waterloo-rocketry/curing-oven/03 - Software/Data/Modular Curing Oven_CD.pdf

# Our Project

A temperature-controlled curing oven for composite materials that is modular, safe, and easy to store

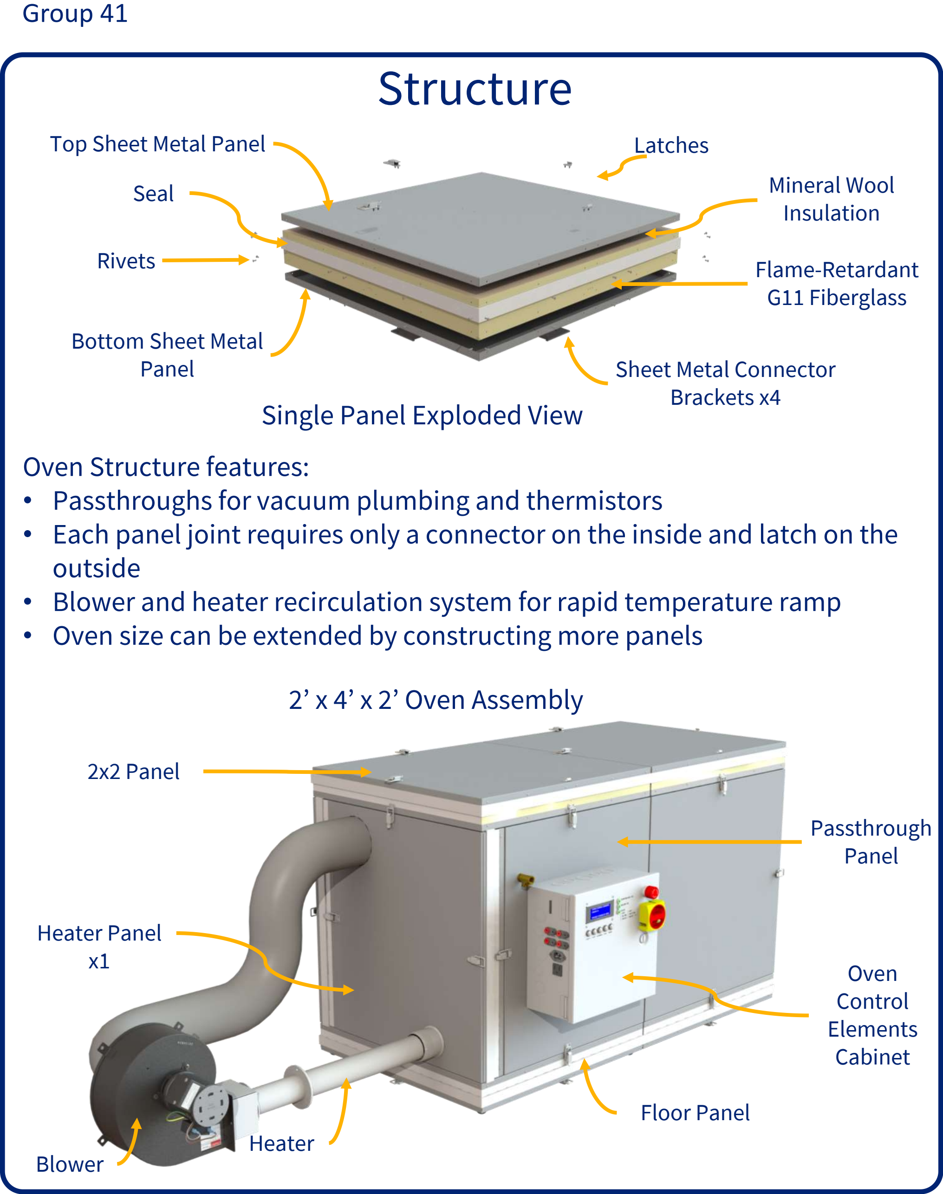
[picture p3: figure]
Group 41; Top Sheet Metal Panel; Latches; Bottom Sheet Metal Panel; Seal; Flame-Retardant G11 Fiberglass; Mineral Wool Insulation; Sheet Metal Connector Brackets x4; Rivets; Single Panel Exploded View; Oven Structure features:; outside; 2’ x 4’ x 2’ Oven Assembly; Blower; Heater; Heater Panel x1; Floor Panel; Oven Control Elements Cabinet; Passthrough Panel; 2x2 Panel
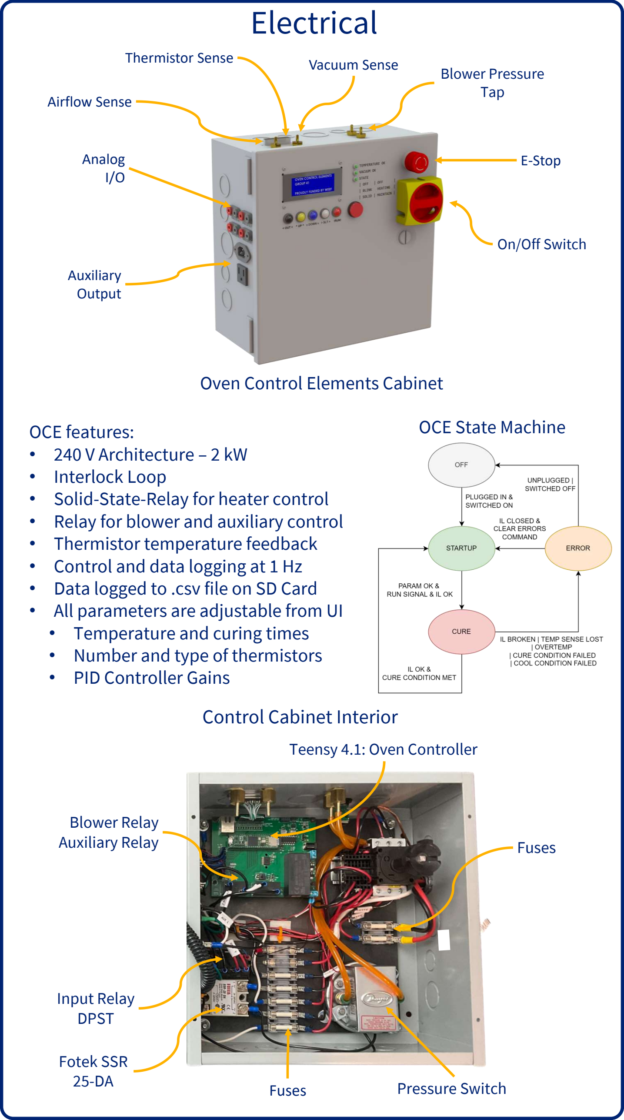
[picture p4: figure]
Control Cabinet Interior; OCE features: • 240 V Architecture – 2 kW • Interlock Loop • Solid-State-Relay for heater control; • Thermistor temperature feedback • Control and data logging at 1 Hz • Data logged to .csv file on SD Card • All parameters are adjustable from UI • Temperature and curing times • Number and type of thermistors • PID Controller Gains; Teensy 4.1: Oven Controller; Blower Relay Auxiliary Relay; Fuses; Pressure Switch; Fotek SSR 25-DA; Input Relay DPST; OCE State Machine; Oven Control Elements Cabinet; Vacuum Sense; Thermistor Sense; Airflow Sense; Blower Pressure Tap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

Structure | Electrical

# Modular Composites Curing Oven

# Testing

# Motivation

- Student design teams in the Sedra Student Design Center at UW work on composites parts that span a wide range of geometries and sizes, and lack the ability to cure parts at temperature
- Most high-performance composite materials must be cured in controlled temperature environments
- Curing ovens are generally expensive, take up large amounts of space, and can be difficult to control

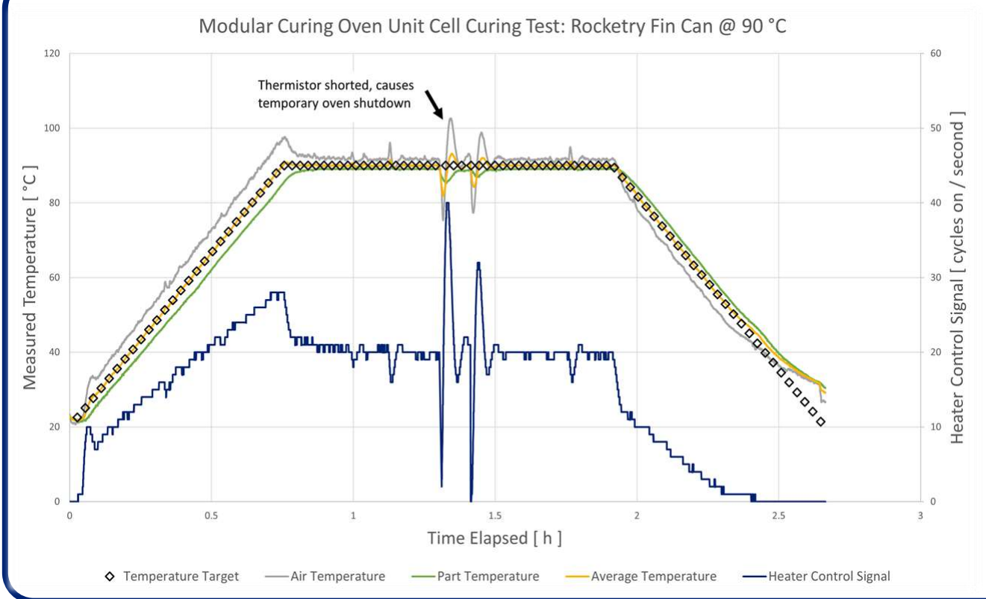
[picture p5: figure]

# Sponsors

Room-sized
industrial oven

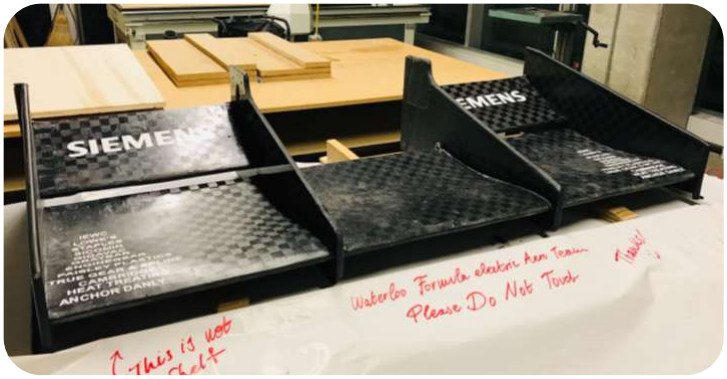
[picture p6: figure]

Low temp
recycling bin oven

High pressure autoclave
for Boeing 77X

# Existing Solutions:

Rocketry Fin Can

Formula Electric Front Wing

Design Objectives | Specifications | Value | Unit | Results
Functionality | Temperature Uniformity | ± 5 | °C | Pass
Functionality | Service Life | ≥ 10 | year | N/A
Functionality | Temperature Ramp Rate | ≥ 2 | °C/min | N/A
Safety | Structure and Ducting Surface Temperature | ≤ 30 | °C | Fail
Safety | Maximum Air Temperature ≤ 200 | °C | Pass
User Friendliness Assembly Time | ≤ 15 | min | Pass

Power Source: 240 V
Resin: Airstone 780E
Cure Schedule: 1 hr
@ 90 °C 45 min.
ramp
Temperature Error:
< 5 °C at steady state

The rocketry fin can was post-cured in the curing oven to obtain better structural properties at the high temperatures observed in the desert at competition in New Mexico.

- Passthroughs for vacuum plumbing and thermistors
- Each panel joint requires only a connector on the inside and latch on the
- Blower and heater recirculation system for rapid temperature ramp
- Oven size can be extended by constructing more panels
- Relay for blower and auxiliary control

Hamza Abu Abah
Calvin DeKoter
Shirley Kong
Nicolas Vrban
Yang Tina Zhang
