waterloo-rocketry/curing-oven/03 - Software/Data/AX-5201XL_curecycle.png

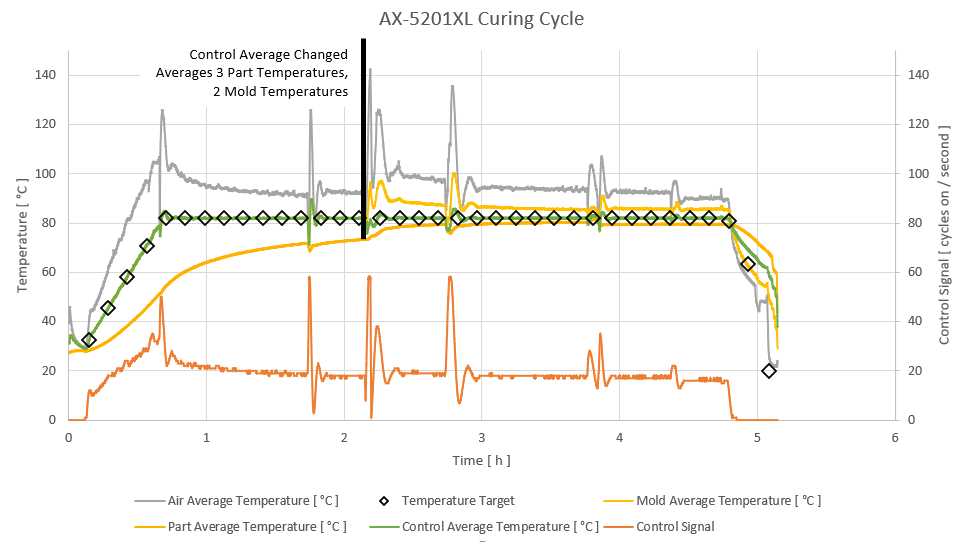
03 - Software/Data/AX-5201XL_curecycle.png
