waterloo-rocketry/curing-oven/03 - Software/Data/fincangraph.png

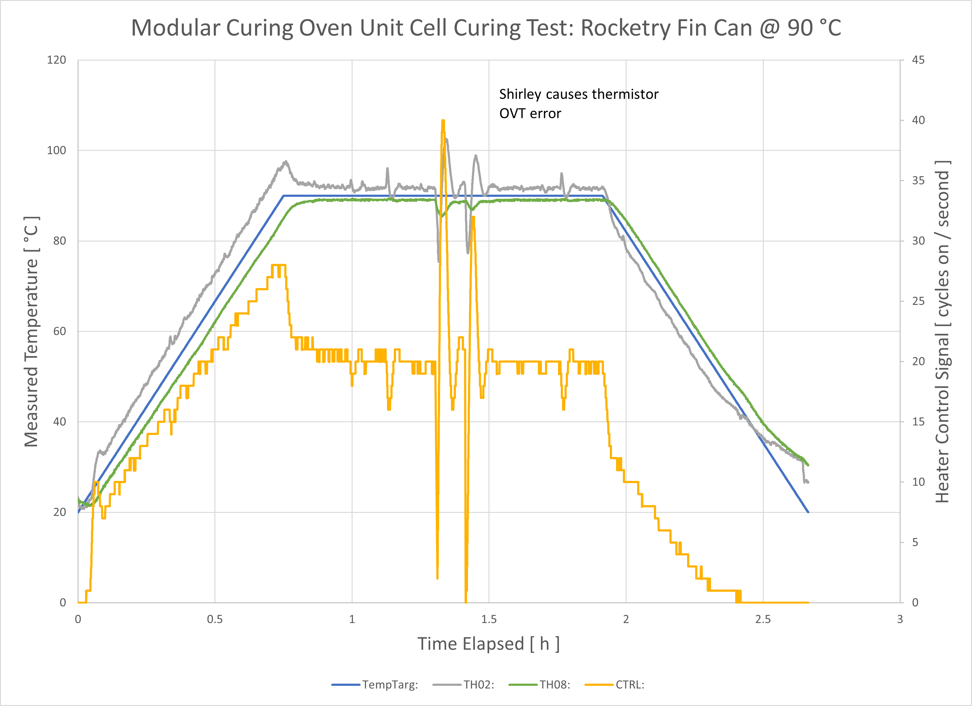
03 - Software/Data/fincangraph.png
