waterloo-rocketry/curing-oven/03 - Software/Data/fincangraph_temperror.png

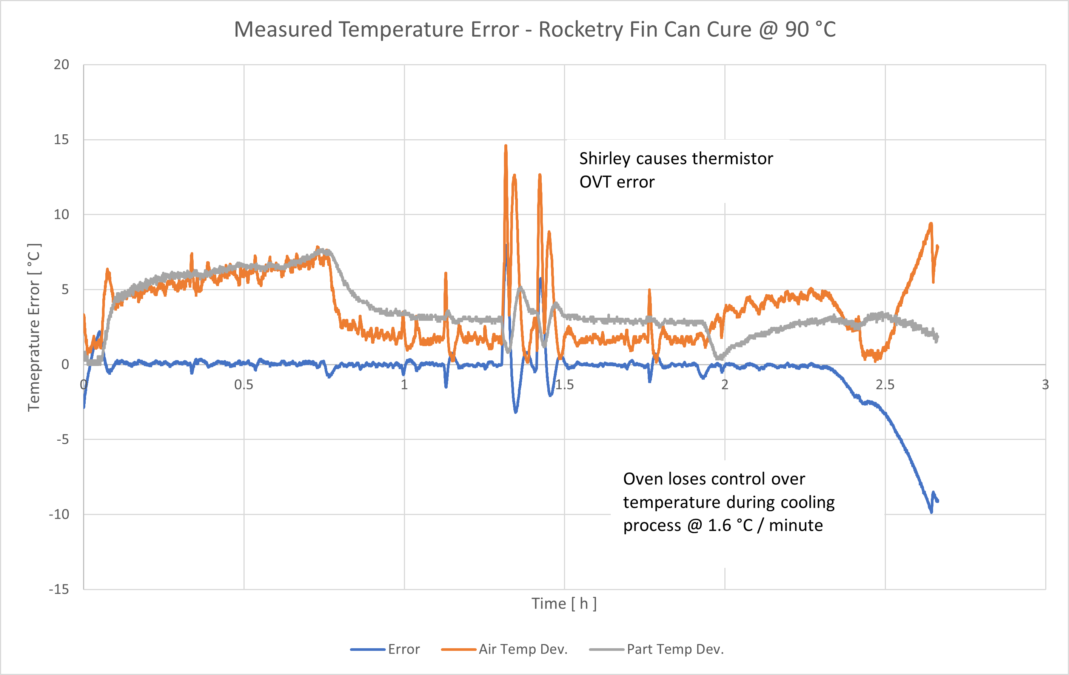
03 - Software/Data/fincangraph_temperror.png
