waterloo-rocketry/curing-oven/03 - Software/Data/fincangraphv2.png

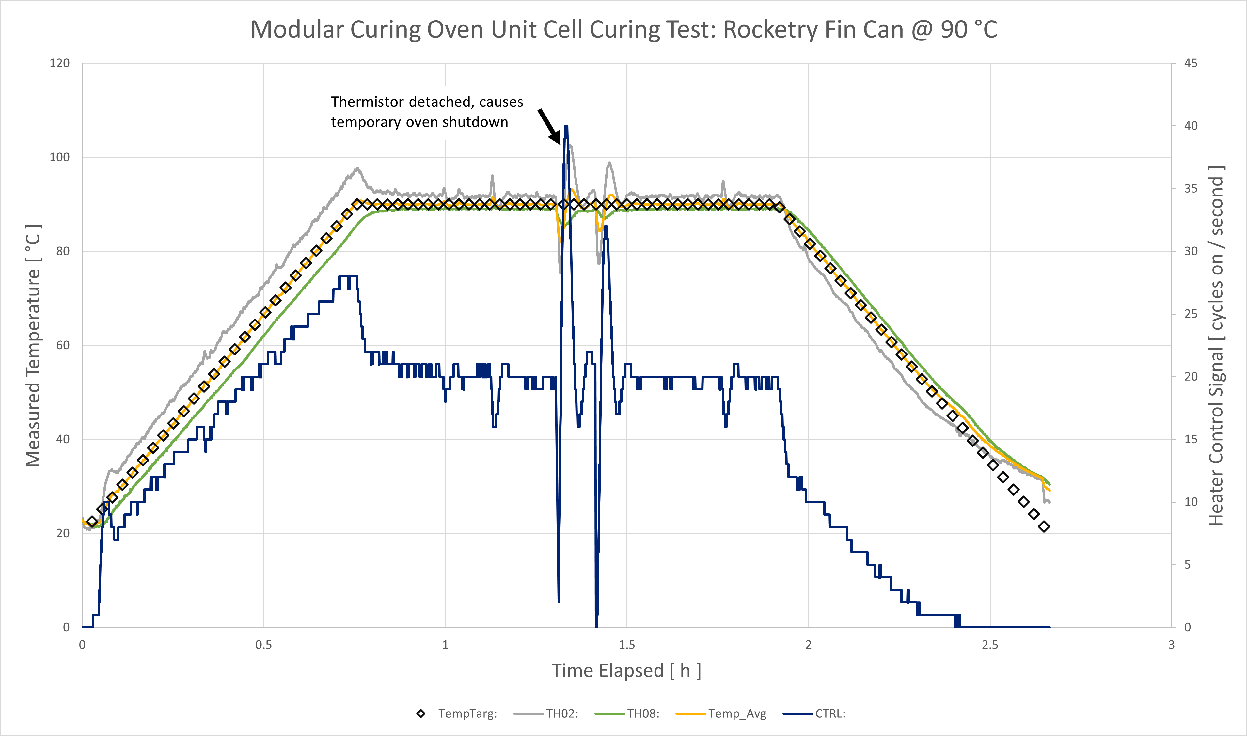
03 - Software/Data/fincangraphv2.png
