waterloo-rocketry/curing-oven/03 - Software/Data/firstplot.png

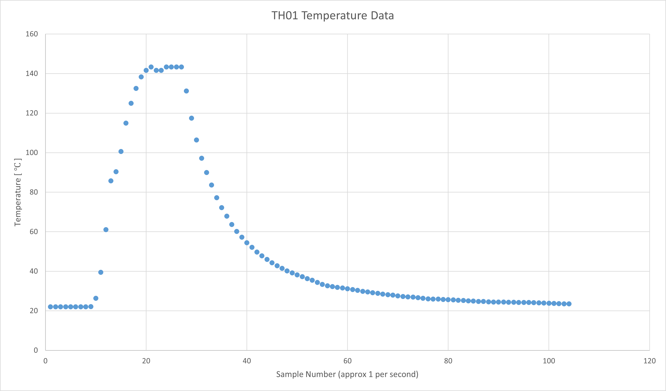
03 - Software/Data/firstplot.png
