waterloo-rocketry/curing-oven/03 - Software/Data/protoplot.png

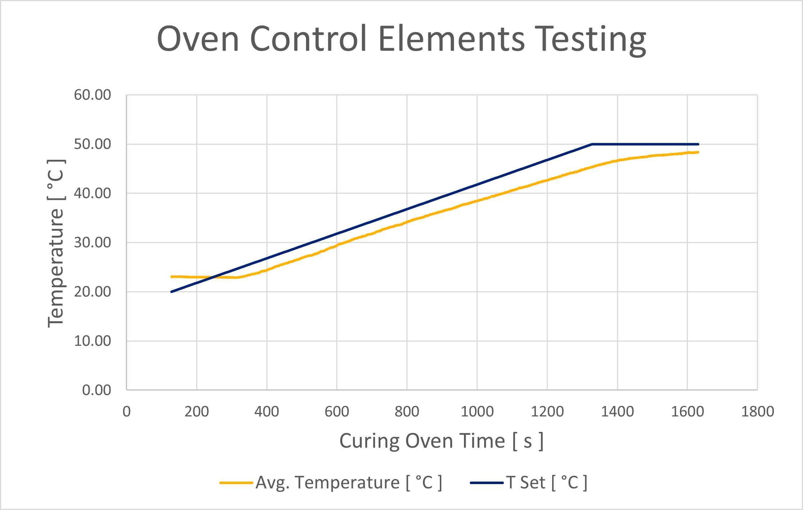
03 - Software/Data/protoplot.png
