waterloo-rocketry/curing-oven/03 - Software/Data/secondplot.png

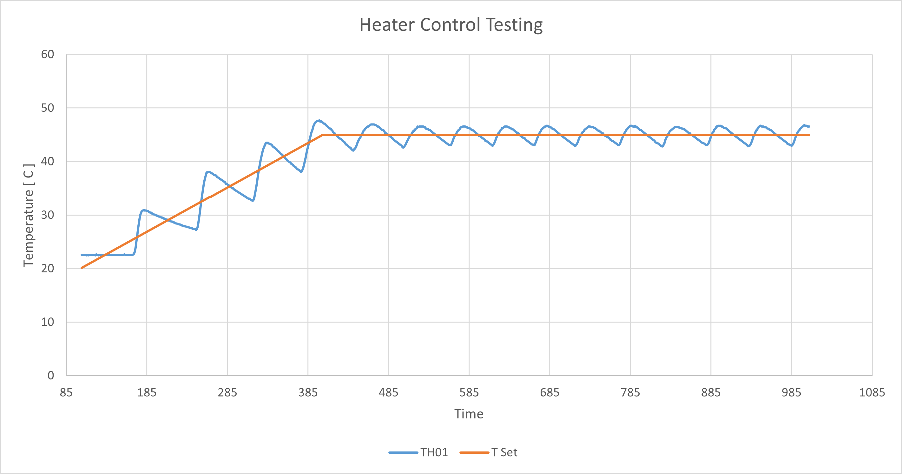
03 - Software/Data/secondplot.png
