waterloo-rocketry/curing-oven/03 - Software/Data/thirdplot.png

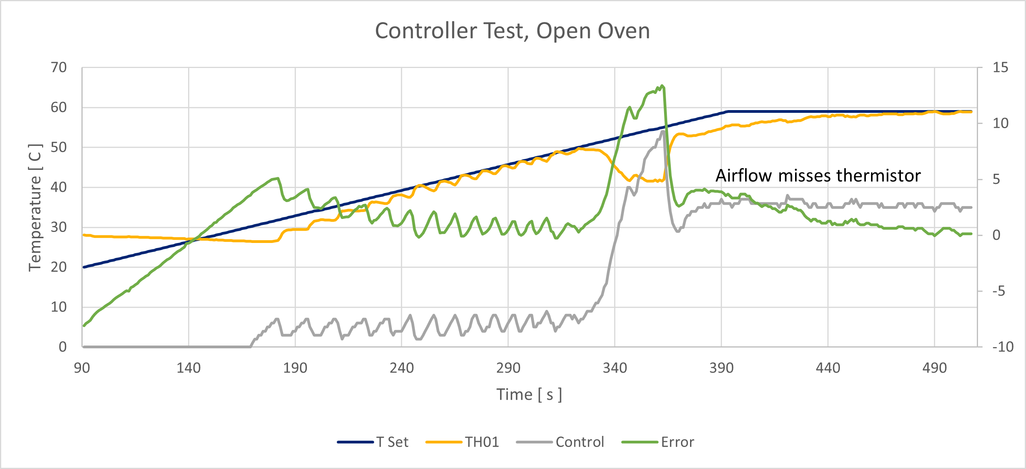
03 - Software/Data/thirdplot.png
