waterloo-rocketry/curing-oven/03 - Software/Data/unitcelltest.png

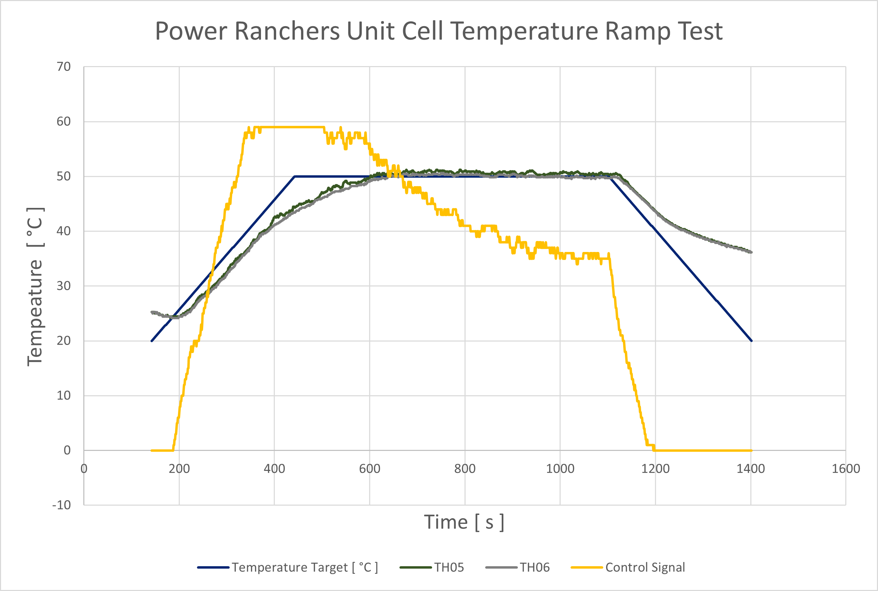
03 - Software/Data/unitcelltest.png
