waterloo-rocketry/curing-oven/03 - Software/OCE_Firmware_V1/Webserver2/Webserver2.ino

/*
  Web Server
 
 A simple web server that shows the value of the analog input pins.
 using an Arduino Wiznet Ethernet shield. 
 
 Circuit:
 * Ethernet shield attached to pins 10, 11, 12, 13
 * Analog inputs attached to pins A0 through A5 (optional)
 
 created 18 Dec 2009
 by David A. Mellis
 modified 9 Apr 2012
 by Tom Igoe
 
 */


#include <NativeEthernet.h>

// Enter a IP address for your controller below.

uint8_t mac[6];
IPAddress ip(192,168,1,177);

// Initialize the Ethernet server library
// with the IP address and port you want to use 
// (port 80 is default for HTTP):
EthernetServer server(80);

// Find Mac address for Teensy
static void teensyMAC(uint8_t *mac) {
  uint32_t m1 = HW_OCOTP_MAC1;
  uint32_t m2 = HW_OCOTP_MAC0;
  mac[0] = m1 >> 8;
  mac[1] = m1 >> 0;
  mac[2] = m2 >> 24;
  mac[3] = m2 >> 16;
  mac[4] = m2 >> 8;
  mac[5] = m2 >> 0;
}


void setup() {
  // Open serial communications and wait for port to open:
  Serial.begin(9600);
   while (!Serial) {
    ; // wait for serial port to connect. Needed for Leonardo only
  }
  Serial.println("About to start Ethernet, apparently the cable needs plugged in before it will proceed!");
  teensyMAC(mac);
  static char teensyMacString[23];
  sprintf(teensyMacString, "MAC: %02x:%02x:%02x:%02x:%02x:%02x", mac[0], mac[1], mac[2], mac[3], mac[4], mac[5]);
  Serial.println(teensyMacString);
  
  // start the Ethernet connection and the server:
  Ethernet.begin(mac, ip);
  server.begin();
  Serial.print("server is at ");
  Serial.println(Ethernet.localIP());
}


void loop() {
  // listen for incoming clients
  EthernetClient client = server.available();
  if (client) {
    Serial.println("new client");
    // an http request ends with a blank line
    boolean currentLineIsBlank = true;
    while (client.connected()) {
      if (client.available()) {
        char c = client.read();
        Serial.write(c);
        // if you've gotten to the end of the line (received a newline
        // character) and the line is blank, the http request has ended,
        // so you can send a reply
        if (c == '\n' && currentLineIsBlank) {
          // send a standard http response header
          client.println("HTTP/1.1 200 OK");
          client.println("Content-Type: text/html");
          client.println("Connection: close");
          client.println();
          client.println("<!DOCTYPE HTML>");
          client.println("<html>");
          // add a meta refresh tag, so the browser pulls again every 5 seconds:
          client.println("<meta http-equiv=\"refresh\" content=\"1\">");
          // output the value of each analog input pin
          for (int analogChannel = 0; analogChannel < 6; analogChannel++) {
            int sensorReading = analogRead(analogChannel);
            client.print("analog input ");
            client.print(analogChannel);
            client.print(" is ");
            client.print(sensorReading);
            client.println("<br />");       
          }
          client.println("</html>");
          break;
        }
        if (c == '\n') {
          // you're starting a new line
          currentLineIsBlank = true;
        } 
        else if (c != '\r') {
          // you've gotten a character on the current line
          currentLineIsBlank = false;
        }
      }
    }
    // give the web browser time to receive the data
    delay(1);
    // close the connection:
    client.stop();
    Serial.println("client disonnected");
  }
}
