waterloo-rocketry/curing-oven/03 - Software/OCE_Firmware_V1/UIPlayground/UIPlayground.ino

//YWROBOT
//Compatible with the Arduino IDE 1.0
//Library version:1.1
//Library to use the SCA2/SCL2 port on the Teensy 4.1
#include <LiquidCrystal_Wire2_I2C.h>

LiquidCrystal_Wire2_I2C lcd(0x27,20,4);  // set the LCD address to 0x27 for a 20 chars and 2 line display

void setup()
{
  lcd.init();                      // initialize the lcd 

  // Print a message to the LCD.
  lcd.backlight();
  lcd.setCursor(3,0);
  lcd.print("Hello, world!");
  lcd.setCursor(2,1);
  lcd.print("Ywrobot Arduino!");
   lcd.setCursor(0,2);
  lcd.print("Arduino LCM IIC 2004");
   lcd.setCursor(2,3);
  lcd.print("Power By Ec-yuan!");
}


void loop()
{
}
